kyleetqi/stockticker/images/IMG_5108.JPG

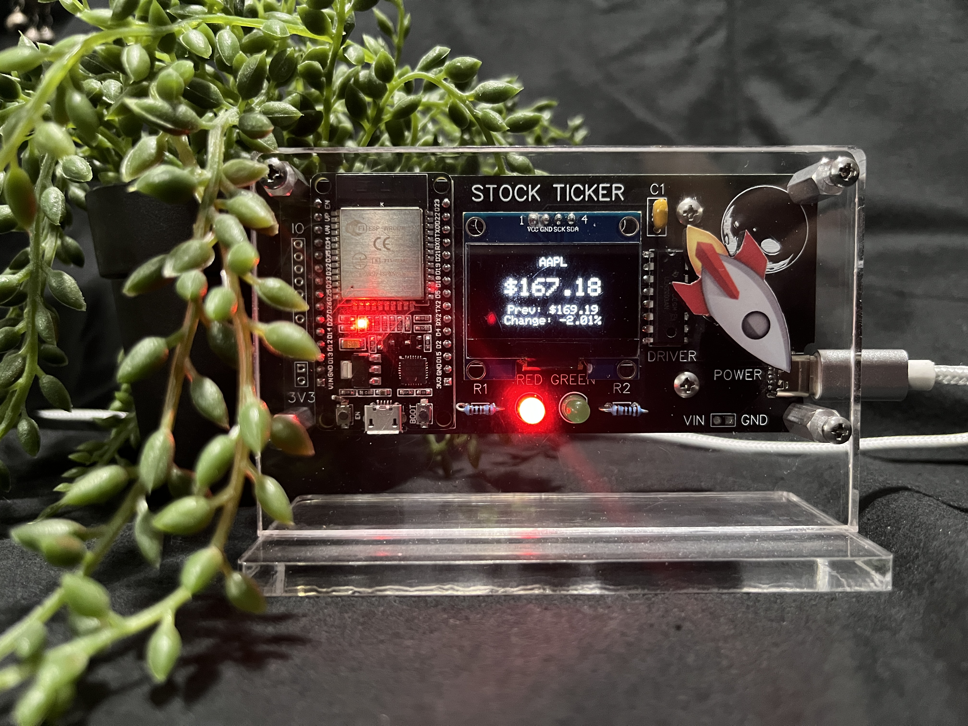
images/IMG_5108.JPG
