kyleetqi/stockticker/images/IMG_5110.JPG

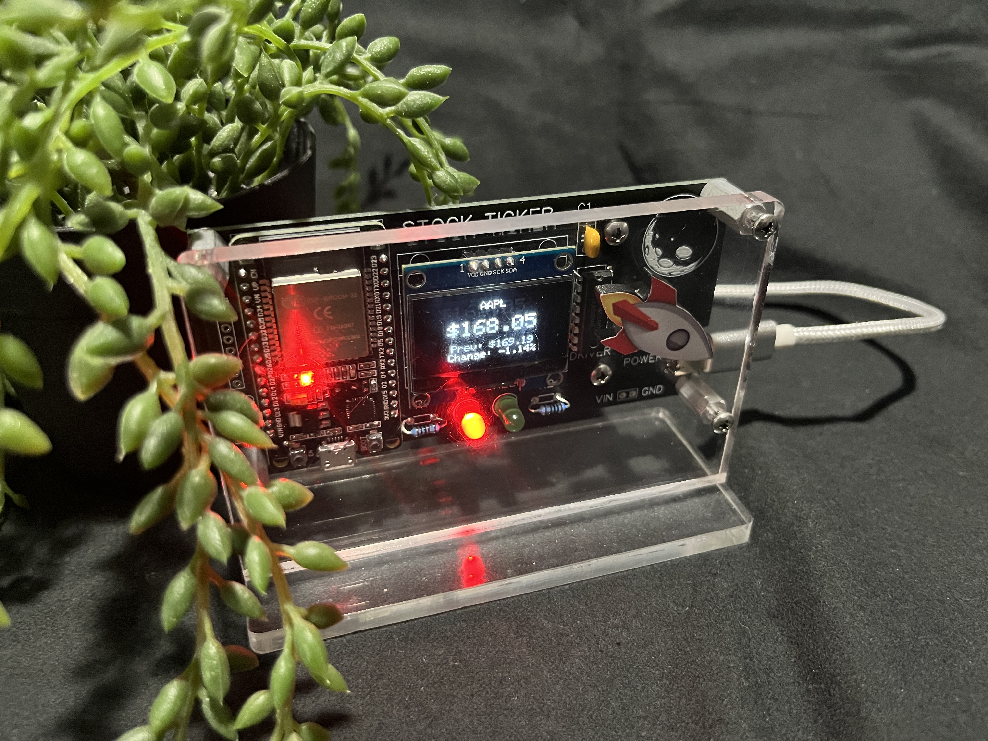
images/IMG_5110.JPG
