kyleetqi/stockticker/images/IMG_5111.JPG

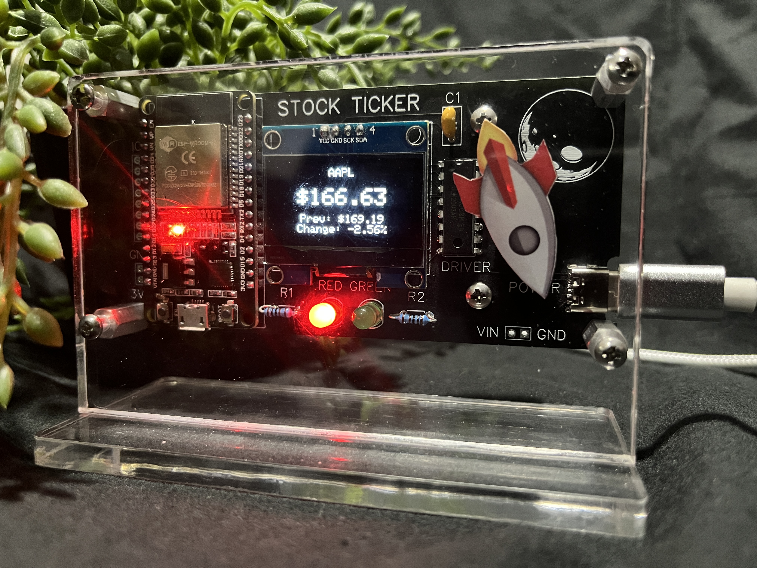
images/IMG_5111.JPG
