kyleetqi/stockticker/images/IMG_5112.JPG

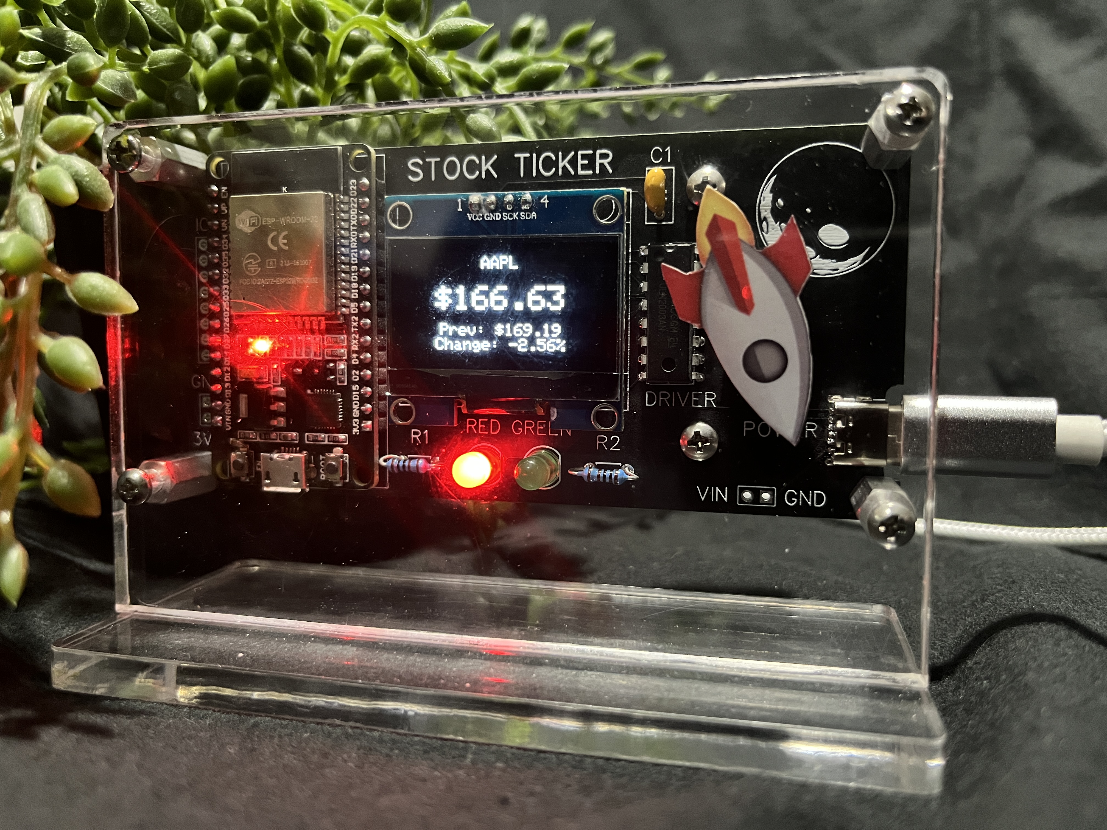
images/IMG_5112.JPG
