kyleetqi/stockticker/images/IMG_5113.JPG

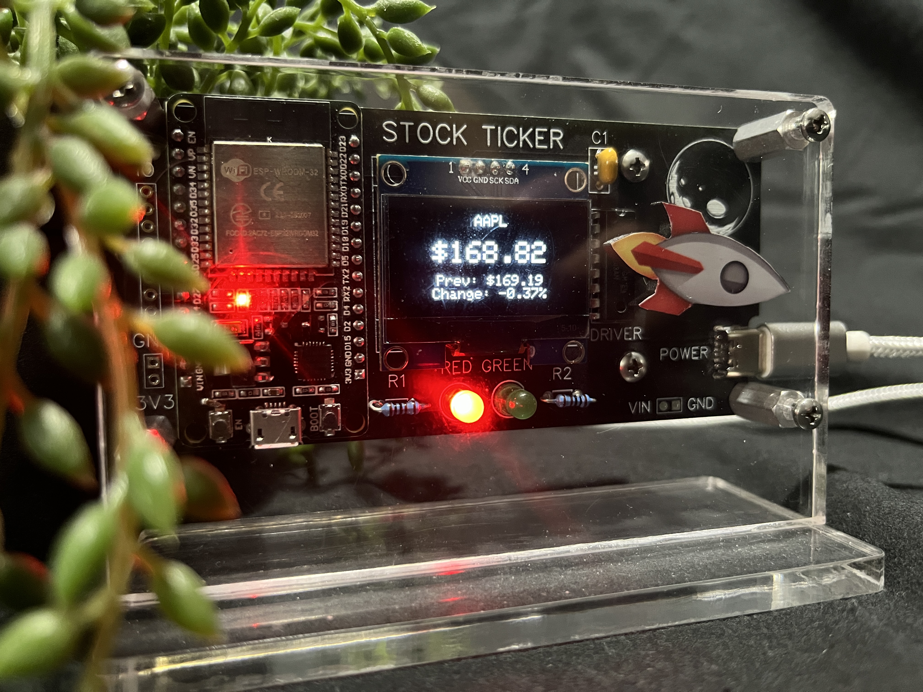
images/IMG_5113.JPG
