kyleetqi/stockticker/images/IMG_5114.JPG

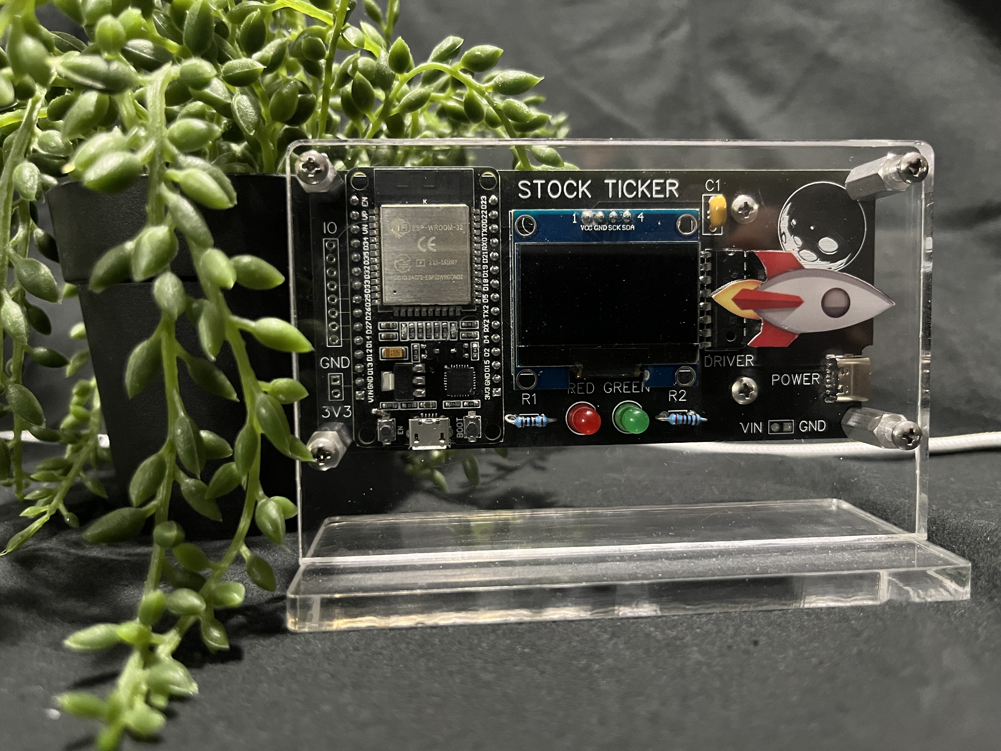
images/IMG_5114.JPG
