kyleetqi/stockticker/images/IMG_5115.JPG

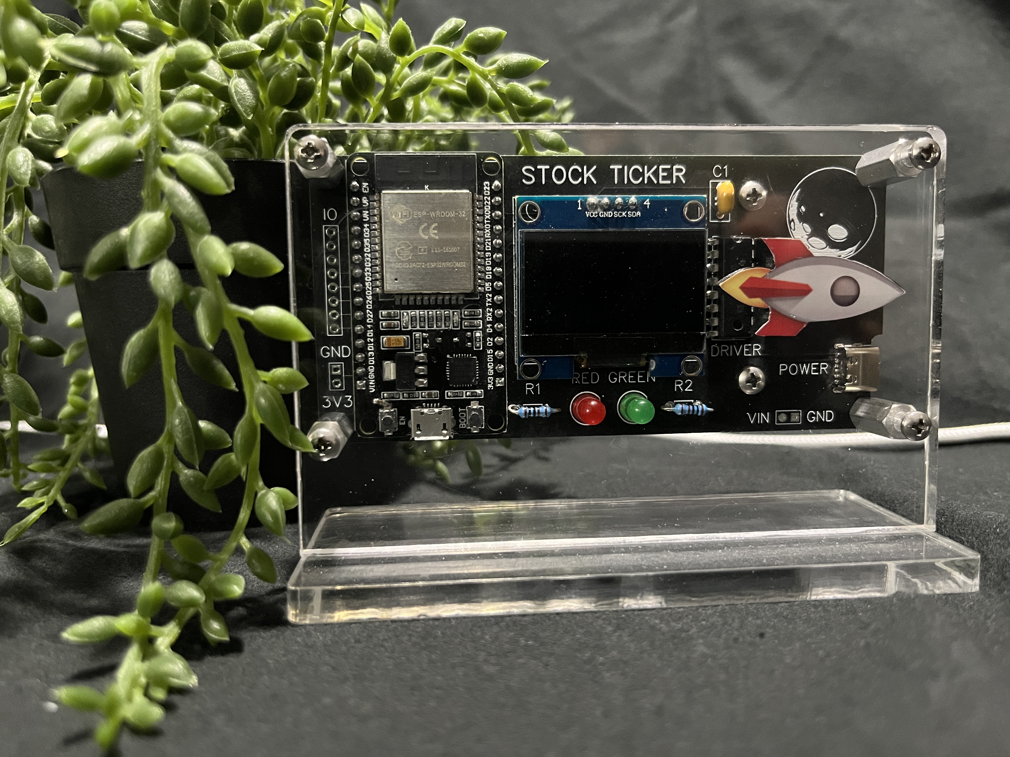
images/IMG_5115.JPG
